sunghyuneun/Autonomous-Drone/CAD/full_assembly_stepper.SLDASM

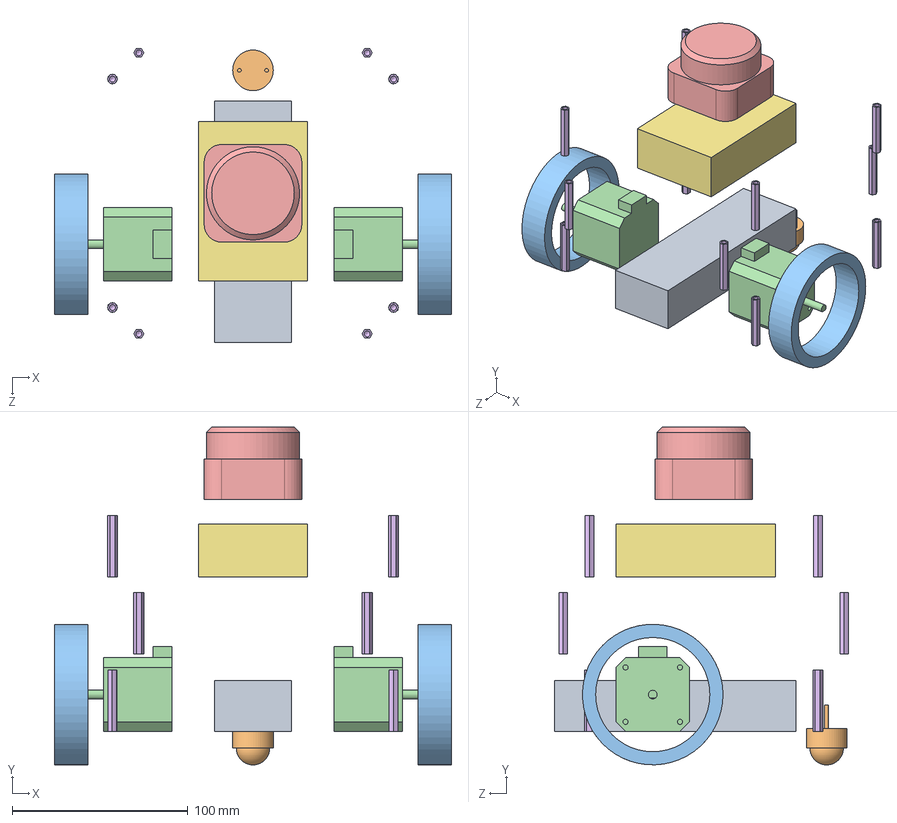
[picture p10: CAD file, 2025-12-09]
CAD/full_assembly_stepper.SLDASM
226.0 x 192.3 x 167.5 mm
raspberry_pi
hex_standoff x 12
lidar
Nema17 x 2
wheel_tire x 2
ball_caster
lipo
