sunghyuneun/Autonomous-Drone/CAD/assembly1_stepper.SLDASM

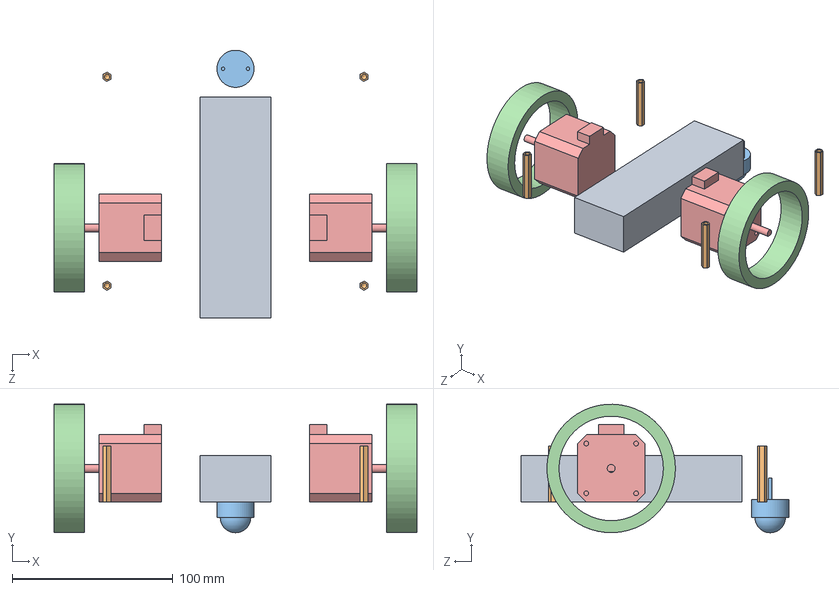
[picture p11: CAD file, 2025-12-09]
CAD/assembly1_stepper.SLDASM
226.0 x 80.0 x 166.6 mm
Nema17 x 2
wheel_tire x 2
ball_caster
hex_standoff x 4
lipo
