sunghyuneun/Autonomous-Drone/CAD/assembly2_stepper.SLDASM

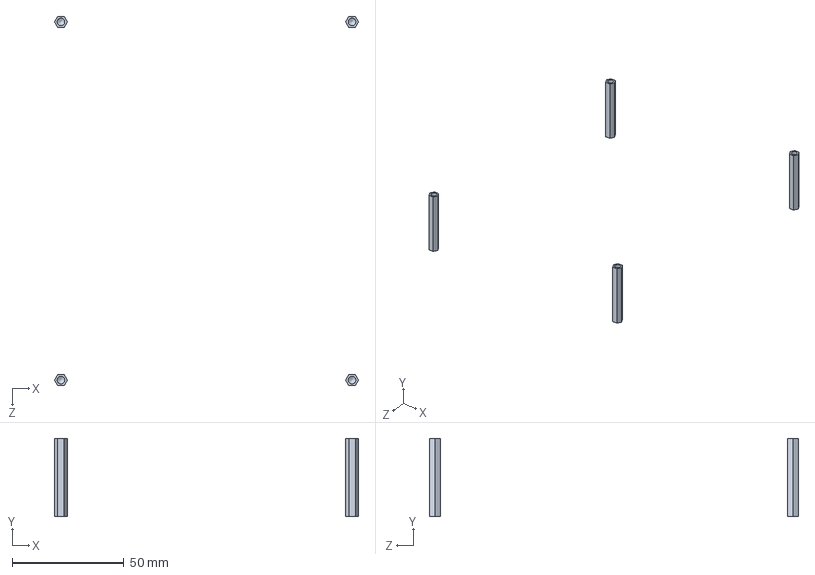
[picture p12: CAD file, 2025-12-09]
CAD/assembly2_stepper.SLDASM
135.8 x 35.0 x 165.0 mm
hex_standoff x 4
