sunghyuneun/Autonomous-Drone/CAD/plates/plate1_stepper.STEP

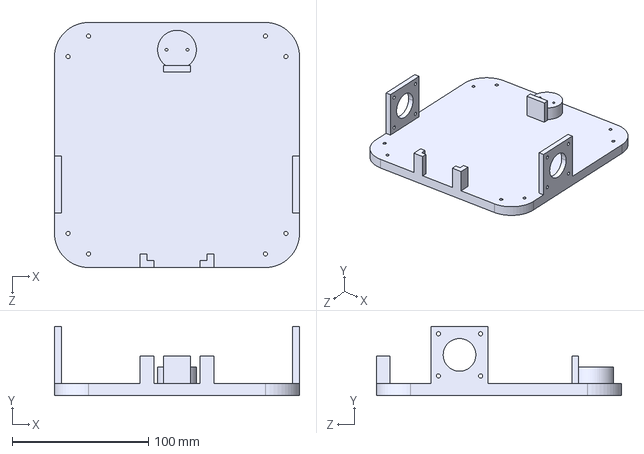
[picture p23: CAD file, 2025-12-08]
CAD/plates/plate1_stepper.STEP
180.0 x 51.0 x 180.0 mm
