sunghyuneun/Autonomous-Drone/CAD/individual parts/raspberry_pi.SLDPRT

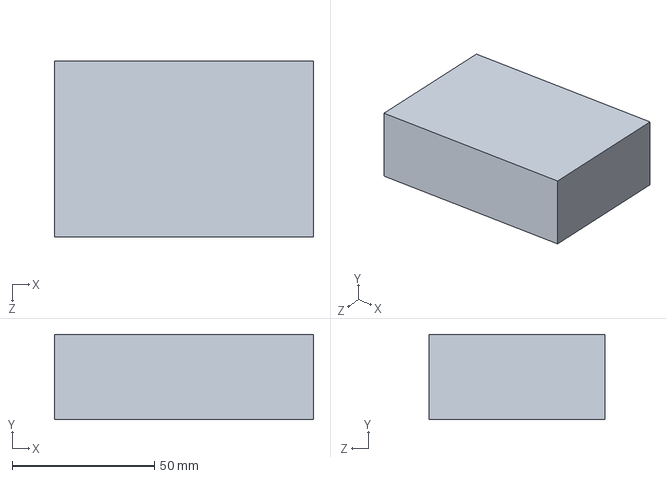
[picture p24: CAD file, 2025-12-11]
CAD/individual parts/raspberry_pi.SLDPRT
91.0 x 30.0 x 62.0 mm
