sunghyuneun/Autonomous-Drone/CAD/plates/plate2_stepper.STEP

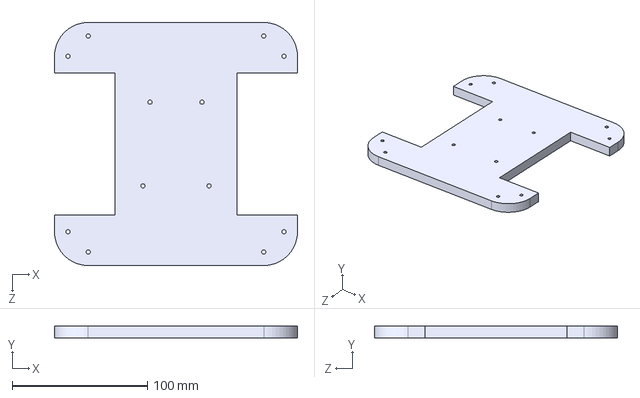
[picture p25: CAD file, 2025-12-08]
CAD/plates/plate2_stepper.STEP
180.0 x 9.00 x 180.0 mm
