sunghyuneun/Autonomous-Drone/CAD/testprint.STEP

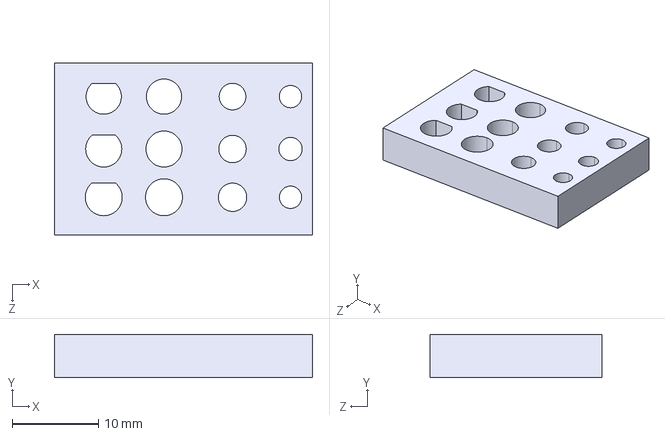
[picture p26: CAD file, 2025-12-13]
CAD/testprint.STEP
30.0 x 5.00 x 20.0 mm
