sunghyuneun/Autonomous-Drone/CAD/individual parts/lipo.SLDPRT

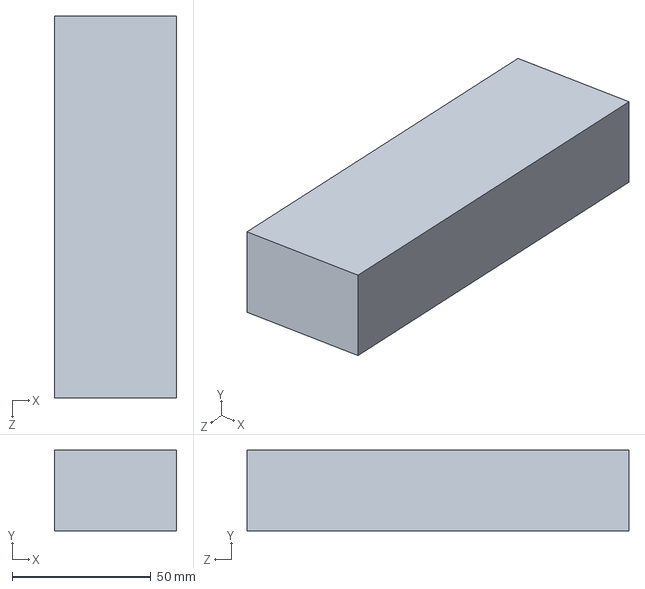
[picture p27: CAD file, 2025-12-08]
CAD/individual parts/lipo.SLDPRT
44.0 x 29.0 x 137.5 mm
