sunghyuneun/Autonomous-Drone/CAD/individual parts/Arduino UNO Rev3_base original.stp

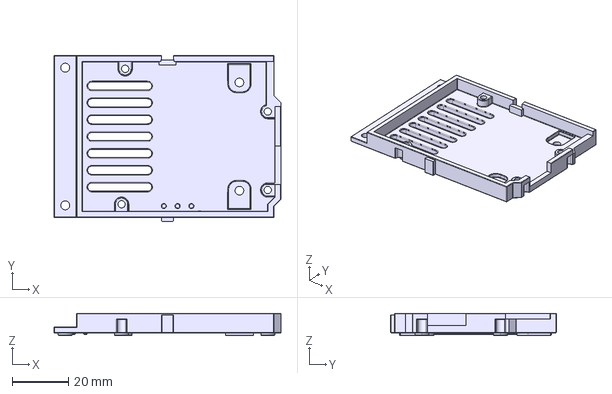
[picture p28: CAD file, 2025-12-07]
CAD/individual parts/Arduino UNO Rev3_base original.stp
80.8 x 59.0 x 8.00 mm
