sunghyuneun/Autonomous-Drone/CAD/pcbtestprint.STEP

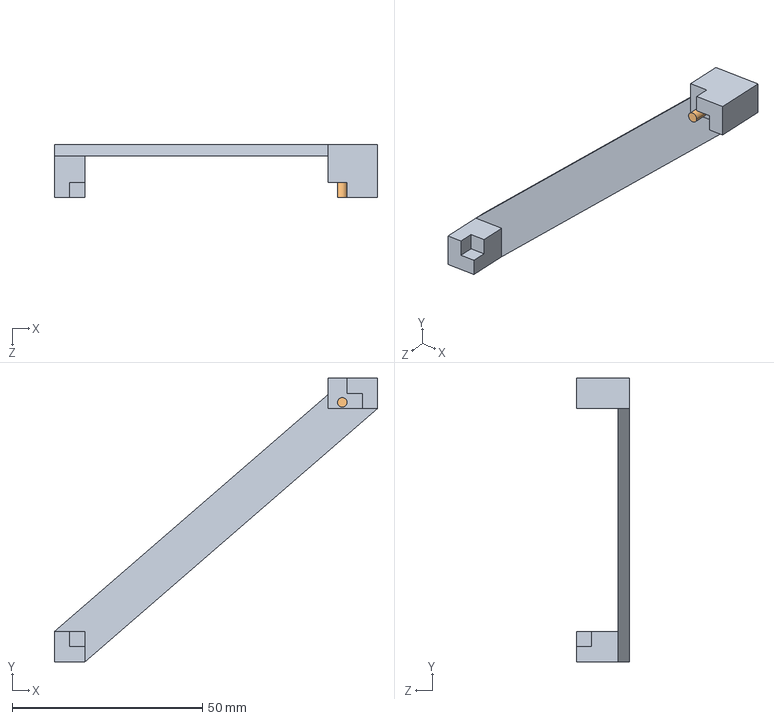
[picture p29: CAD file, 2025-12-09]
CAD/pcbtestprint.STEP
84.8 x 74.5 x 14.0 mm
