sunghyuneun/Autonomous-Drone/CAD/individual parts/RPLidar C1.stp

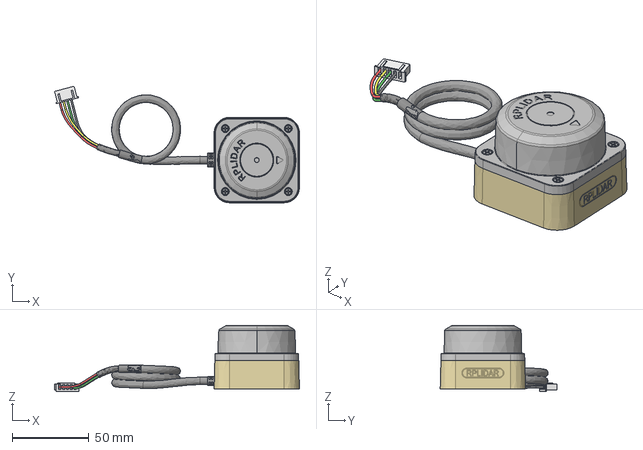
[picture p30: CAD file, 2025-12-07]
CAD/individual parts/RPLidar C1.stp
159.5 x 75.9 x 43.1 mm
