sunghyuneun/Autonomous-Drone/CAD/individual parts/lidar.SLDPRT

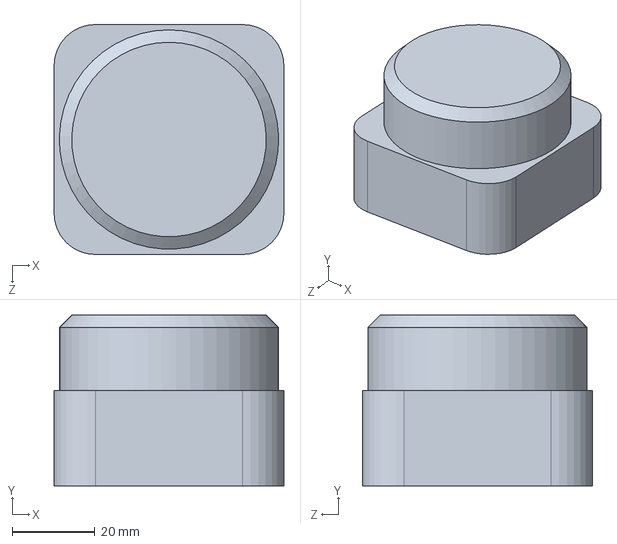
[picture p31: CAD file, 2025-12-07]
CAD/individual parts/lidar.SLDPRT
55.6 x 41.3 x 55.6 mm
