sunghyuneun/Autonomous-Drone/CAD/individual parts/Nema17.SLDPRT

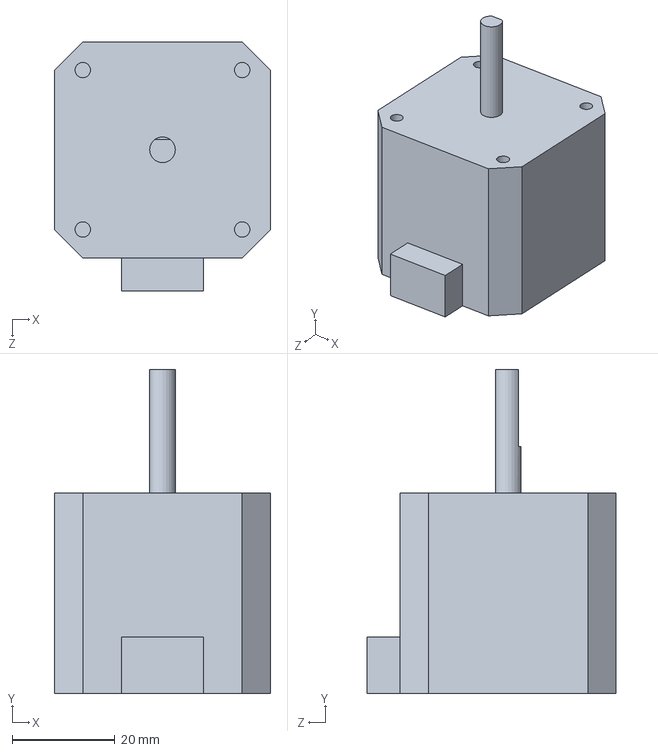
[picture p32: CAD file, 2025-12-06]
CAD/individual parts/Nema17.SLDPRT
42.0 x 63.0 x 48.5 mm
