sunghyuneun/Autonomous-Drone/CAD/individual parts/GearMotor.SLDPRT

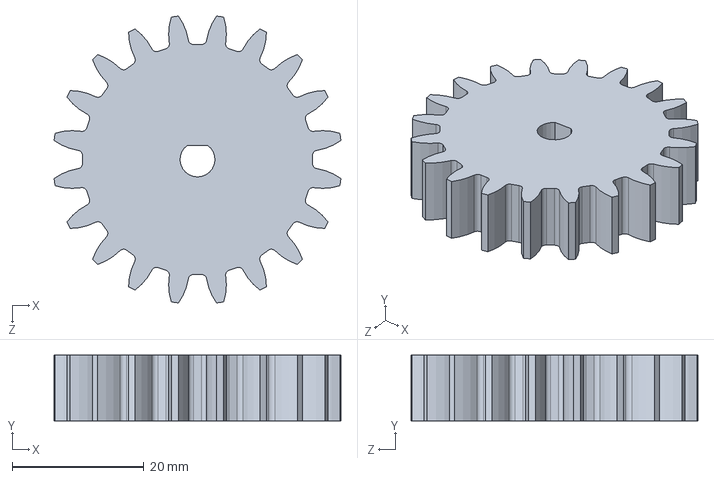
[picture p33: CAD file, 2025-12-06]
CAD/individual parts/GearMotor.SLDPRT
43.6 x 10.0 x 43.6 mm
