sunghyuneun/Autonomous-Drone/CAD/individual parts/hex_standoff.SLDPRT

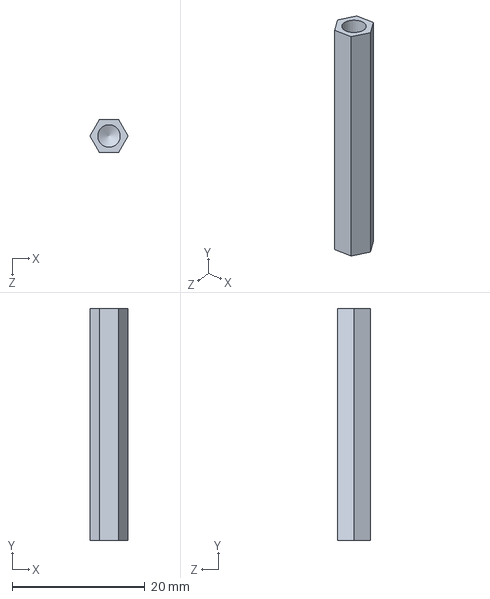
[picture p34: CAD file, 2025-12-03]
CAD/individual parts/hex_standoff.SLDPRT
5.77 x 35.0 x 5.00 mm
