sunghyuneun/Autonomous-Drone/CAD/individual parts/wheel_tire.SLDPRT

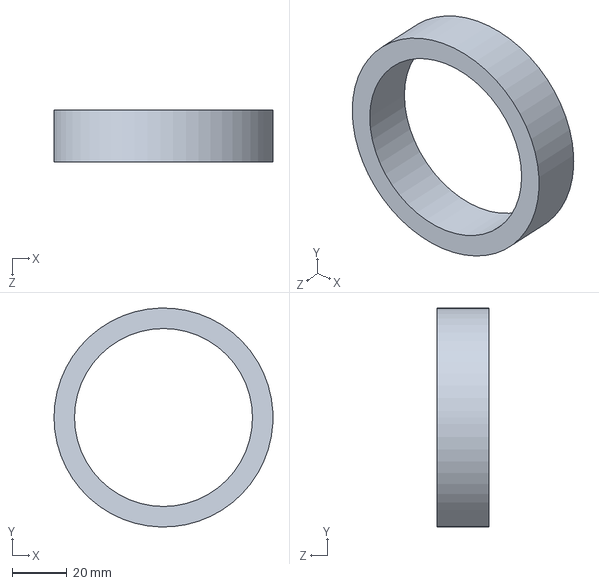
[picture p35: CAD file, 2025-12-03]
CAD/individual parts/wheel_tire.SLDPRT
80.0 x 80.0 x 19.0 mm
