sunghyuneun/Autonomous-Drone/CAD/assembly4.SLDASM

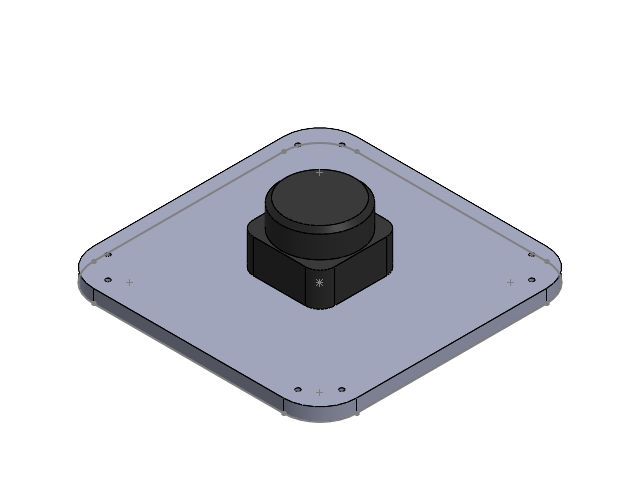
[picture p37: CAD file, 2025-12-13]
CAD/assembly4.SLDASM
plate4
lidar
